bartlettD/nixie-clock/Simulation/NewBoostUCC3803.asc

C1: cap; 1µ
C2: cap; 10µ
C3: cap; 7.54p
C4: cap; 100n
C5: cap; 250p
C6: cap; 1µ
D1: diode; D1n4004rl
D2: diode; D1n4004rl
D3: diode; D1n4004rl
L1: ind; 82µ
M1: nmos; IPL65R070C7_L1
R1: res; 12k
R2: res; 0.0162
R4: res; 140m
R5: res; 54.9k
R6: res; 10
R7: res; 100k
R8: res; 1Meg
R9: res; 11.285k
R11: res; 0.5
U1: UCC3803
V1: voltage; PWL(0 0 1u 5); Rser=15m
V2: voltage; PULSE(0 5 0 10n 10n 0.0000125 0.000025)
Named nets: 0, IN, OUT, CS, FB, VIN, VDRV, OSC, GATE, SW
.lib models\\Infineon_Simulation Model_CoolMOS_C7_MOSFET_650V_Spice.lib
.tran 15m
2.684W Input
2.625W Output
.lib models\\1N4004RL.LIB
Model Includes
.lib models\\SDR1307-820KL.lib
.model STP50NF25 VDMOS(Rg=1.1 Rd=5m Rs=1m Vto=3 Kp=20 Cgdmax=1200p Cgdmin=30p Cgs=1.9n Cjo=1n Is=2.3p Rb=6m mfg=Fairchild Vds=250 Ron=15m Qg=27n)
.model MYSW SW(Ron=1m Roff=1Meg Vt=180 Vh=5)
