bartlettD/nixie-clock/Simulation/NewBoost.asc

C1: cap; 100n
C2: cap; 4.7µ
C3: cap; 7.54p
D1: diode; D1n4004rl
L1: ind; 82µ
L2: ind; 200n
M1: nmos; IPL65R070C7_L1
R1: res; 12k
R2: res; 0.0162
R3: res; 100m
R4: res; 140m
R5: res; 54.9k
V1: voltage; PWL(0 0 1u 5); Rser=15m
V2: voltage; PULSE(0 12 10u 15n 15n 0.00002075 0.000025)
Named nets: 0, IN, OUT
.lib models\\Infineon_Simulation Model_CoolMOS_C7_MOSFET_650V_Spice.lib
.tran 4m
2.684W Input
2.625W Output
.lib models\\1N4004RL.LIB
Model Includes
.lib models\\SDR1307-820KL.lib
