bartlettD/nixie-clock/Simulation/SimpleBoost.asc

C1: cap; 10µ
D2: diode
L1: ind; 82e-6
R1: res; 1
R2: res; 10k
S1: sw; MYSW
V1: voltage; 5
V2: voltage; PULSE(0 10 0 0 0 0.00001 0.00002)
Named nets: 0
.tran 500m
.model MYSW SW(Ron=40e-3 Roff=1Meg Vt=.5 Vh=-.4)
