bartlettD/nixie-clock/Simulation/LM3478_Nixie_Boost.asc

C1: cap; 100µ
C2: cap; 0.01µ
C3: cap; 200µ
C4: cap; 22n
D1: schottky; DFLS220L
L1: ind; 150µ; Rser=10m
M1: nmos; IRFH5053
R1: res; 0.025
R4: res; 4.7k
R5: res; 40k
Rf1: res; {Rf1Val}
Rf2: res; {Rf2Val}
U1: LM3478_TRANS
V1: voltage; 12
Named nets: 0
.tran 5m
.param Vout=85 Rf1Val=1Meg Rf2Val='(1.26*Rf1Val) /(Vout-1.26)'
.meas ResF2 PARAM Rf2Val
Program Output Voltage
