bartlettD/nixie-clock/Simulation/ChargePumpDoubler.asc

C1: cap; 0.22µ; Rser=10
C2: cap; 0.22µ; V=250 Rser=10
C3: cap; 1µ; Rser=1
D1: diode; RF101L2S
D2: diode; RF101L2S
D3: diode; RF101L2S
R1: res; 3.4k
V1: voltage; PULSE(0 85 0 0 0 0.000005 0.00001)
Named nets: 0, Vout, Vin
.tran 1m
High ESR Caps needed to limit current
