bartlettD/nixie-clock/Simulation/NixieBoost.asc

C1: cap; 0.22µ; Rser=10
C2: cap; 10µ
C3: cap; 0.22µ; Rser=10
C4: cap; 1µ
D1: diode; MMSD4148
D2: diode; MMSD4148
D3: diode; MMSD4148
L1: ind; 150µ
M1: nmos; IXFX90N30
R1: res; 3.4k
V1: voltage; 12
V2: voltage; PULSE(0 12 0 0 0 0.0000085 0.00001)
Named nets: 0
.tran 1m
